Hardware7253/lcr/Code/main_csrc/system/system.c

#include "system.h"
#include "stm32g4xx_hal.h"

// Get stuck in a while loop incase of an error
// This can easily be detected when debugging
void error_handler(HAL_StatusTypeDef status) {
  while (status != HAL_OK) (void) 0;
}

// Get stuck in a while loop incase of an error
// Also takes a pointer to an error message to be viewed by the debugger
void error_handler_msg(HAL_StatusTypeDef status, volatile char* msg) {
    while (status != HAL_OK) (void) msg;
}

// Init clocks so:
// SYSCLK = 104 MHz
// HCLK   = 104 MHz
// PCLK1  = 104 MHz
// PCLK2  = 104 MHz
void init_clocks(void) {
    // Oscillator config
    {
        RCC_PLLInitTypeDef pll_cfg = {
            .PLLState = RCC_PLL_ON,
            .PLLSource = RCC_PLLSOURCE_HSE,
            .PLLM = RCC_PLLM_DIV1,
            .PLLN = 26,
            .PLLP = RCC_PLLP_DIV2,
            .PLLQ = RCC_PLLQ_DIV2,
            .PLLR = RCC_PLLR_DIV2,
        };

        // Turn on HSE
        // Leave LSI and HSI untouched
        RCC_OscInitTypeDef osc_cfg;
        osc_cfg.OscillatorType = RCC_OSCILLATORTYPE_HSE;
        osc_cfg.HSEState = RCC_HSE_ON;
        osc_cfg.PLL = pll_cfg;
        error_handler_msg(HAL_RCC_OscConfig(&osc_cfg), "Error with oscillator config");
    }

    // Clock config
    {
        RCC_ClkInitTypeDef clk_cfg = {
            .ClockType = RCC_CLOCKTYPE_SYSCLK | RCC_CLOCKTYPE_HCLK | RCC_CLOCKTYPE_PCLK1 | RCC_CLOCKTYPE_PCLK2,
            .SYSCLKSource = RCC_SYSCLKSOURCE_PLLCLK,
            .AHBCLKDivider = RCC_SYSCLK_DIV1,
            .APB1CLKDivider = RCC_HCLK_DIV1,
            .APB2CLKDivider = RCC_HCLK_DIV1,
        };
        error_handler_msg(HAL_RCC_ClockConfig(&clk_cfg, FLASH_ACR_LATENCY_4WS), "Error with clock config");
    }
}

// Returns the tick frequency of the systick interrupt in Hz
uint32_t get_tick_frequency(void) {
    return 1000 / HAL_GetTickFreq();
}

extern void SysTick_Handler(void) {
    HAL_IncTick();
}
