Hardware7253/lcr/Code/main_csrc/measure/range_resistor.h

#pragma once

// Values the main range resistors can take
// Ordered from most to least likely to find the correct range (most likely = 5K)
typedef enum {
    RR_5K = 0,
    RR_100,
    RR_100K,
    NO_RRS,
} range_resistor_t;

// Values the gain resistor can take for the test voltage amplifier opamp
// Ordered from most to least likely to find the correct range (most likely = 10K)
typedef enum {
    GR_10K = 0,
    GR_100K,
    NO_GRS,
} gain_resistor_t;

// Defaults are the range/gain resistors that are selected without
// applying any voltage to the selector relay coils
extern const range_resistor_t RR_DEFAULT;
extern const gain_resistor_t GR_DEFAULT;

void init_range_resistors(void);
float set_range_resistor(range_resistor_t rr);
float set_gain_resistor(gain_resistor_t gr);
